dmachard/open-pixelart/imgs/circuit_v0.png

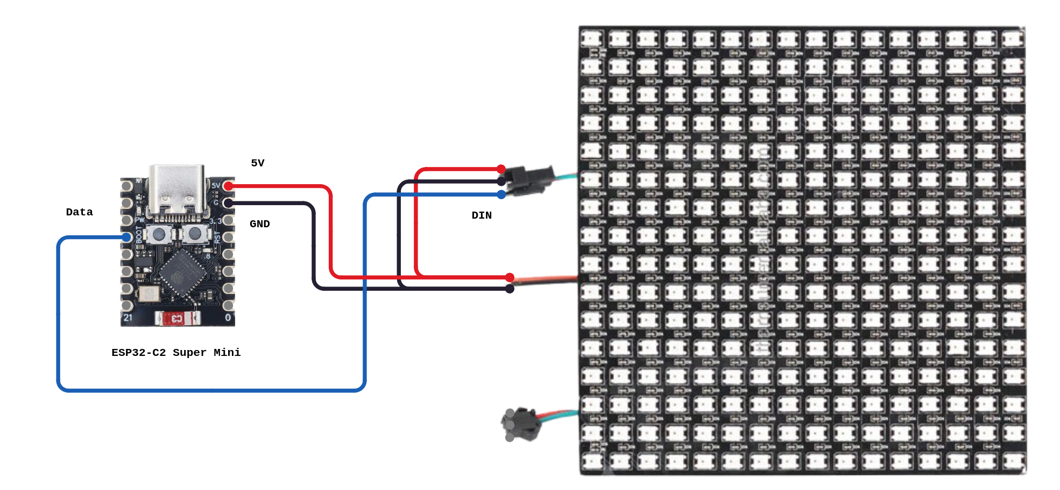
imgs/circuit_v0.png
