dmachard/open-pixelart/firmware/src/decoder.h

#ifndef DECODER_H
#define DECODER_H

#include "config.h"
#include <Arduino.h>

#define FRAMEDEC_HEADER_SIZE 8
#define FRAMEDEC_MAX_PALETTE 16
#define FRAMEDEC_BYTES_PER_ROW (MATRIX_WIDTH / 2)

#define MODE_DRAW 0
#define MODE_GALLERY 1
#define MODE_SETTINGS 2
#define MODE_CLOCK 3
#define MODE_AUDIO 4
#define MODE_GAME 5
#define MODE_TEXT 6
#define MODE_NIGHTLIGHT 7

// Buffer size calculation:
// 16x16: 8 (header) + 48 (palette) + (16x16/2) = 184 bytes
// 64x64: 8 (header) + 48 (palette) + (64x64/2) = 2104 bytes
#define MAX_FRAME_BUFFER_SIZE                                                  \
  (FRAMEDEC_HEADER_SIZE + (16 * 3) + (MATRIX_WIDTH * MATRIX_HEIGHT / 2) + 64)

struct Pixel {
  uint8_t r, g, b;
};

struct Frame {
  Pixel pixels[MATRIX_HEIGHT][MATRIX_WIDTH];
  uint8_t spectrum[16];
  uint8_t gameData[128];
  char textMsg[128];
  Pixel textColor;
  uint8_t textSpeed;
  uint8_t audioStyle;
  uint16_t duration_ms;
  uint8_t brightness;
  uint8_t deviceMode;
  uint8_t frameIndex;
  uint8_t frameTotal;
  uint8_t fontIndex;
};

class FrameDecoder {
private:
  uint8_t frameBuffer[MAX_FRAME_BUFFER_SIZE];
  size_t currentSize = 0;
  uint8_t expectedFragments = 0;
  uint8_t receivedFragments = 0;
  uint32_t lastFragmentTime = 0;

  bool isFragmented(const uint8_t *data, size_t len);
  bool handleFragment(const uint8_t *data, size_t len);

public:
  bool decode(Frame &out, const uint8_t *data, size_t len);
  void checkTimeout();
  uint32_t totalFrames = 0;
  uint32_t droppedFrames = 0;
};

#endif
