dmachard/open-pixelart/firmware/src/text.h

#ifndef TEXT_H
#define TEXT_H

#include "display.h"
#include <Arduino.h>

void initText();
void updateText();
void setText(const char *msg, Pixel color, uint8_t speed, uint8_t fontIndex);
void drawText();

#endif // TEXT_H
